asadpetwalker/CertamenBuzzers/code/main/pinout.h

//BUTTON BUZZER PINS
#define A1 5
#define A2 6
#define A3 7
#define A4 8

#define B1 9
#define B2 10
#define B4 11
#define B3 12

#define C1 13
#define C2 14
#define C3 15
#define C4 16

//SCOREBOARD BUTTONS
#define SCA 1
#define SCB 0
#define SCC 28

//BUZZER BUZZER PINS
#define BZ1 17
#define BZ2 18
#define BZ3 19
#define BZ4 20

//CONSOLE RESET BUTTON
#define RESET 4
